ScatteredDrifter/BullIso/pcb/pcb.kicad_sch

## KiCad design pcb/pcb.kicad_sch (2023-05-31)

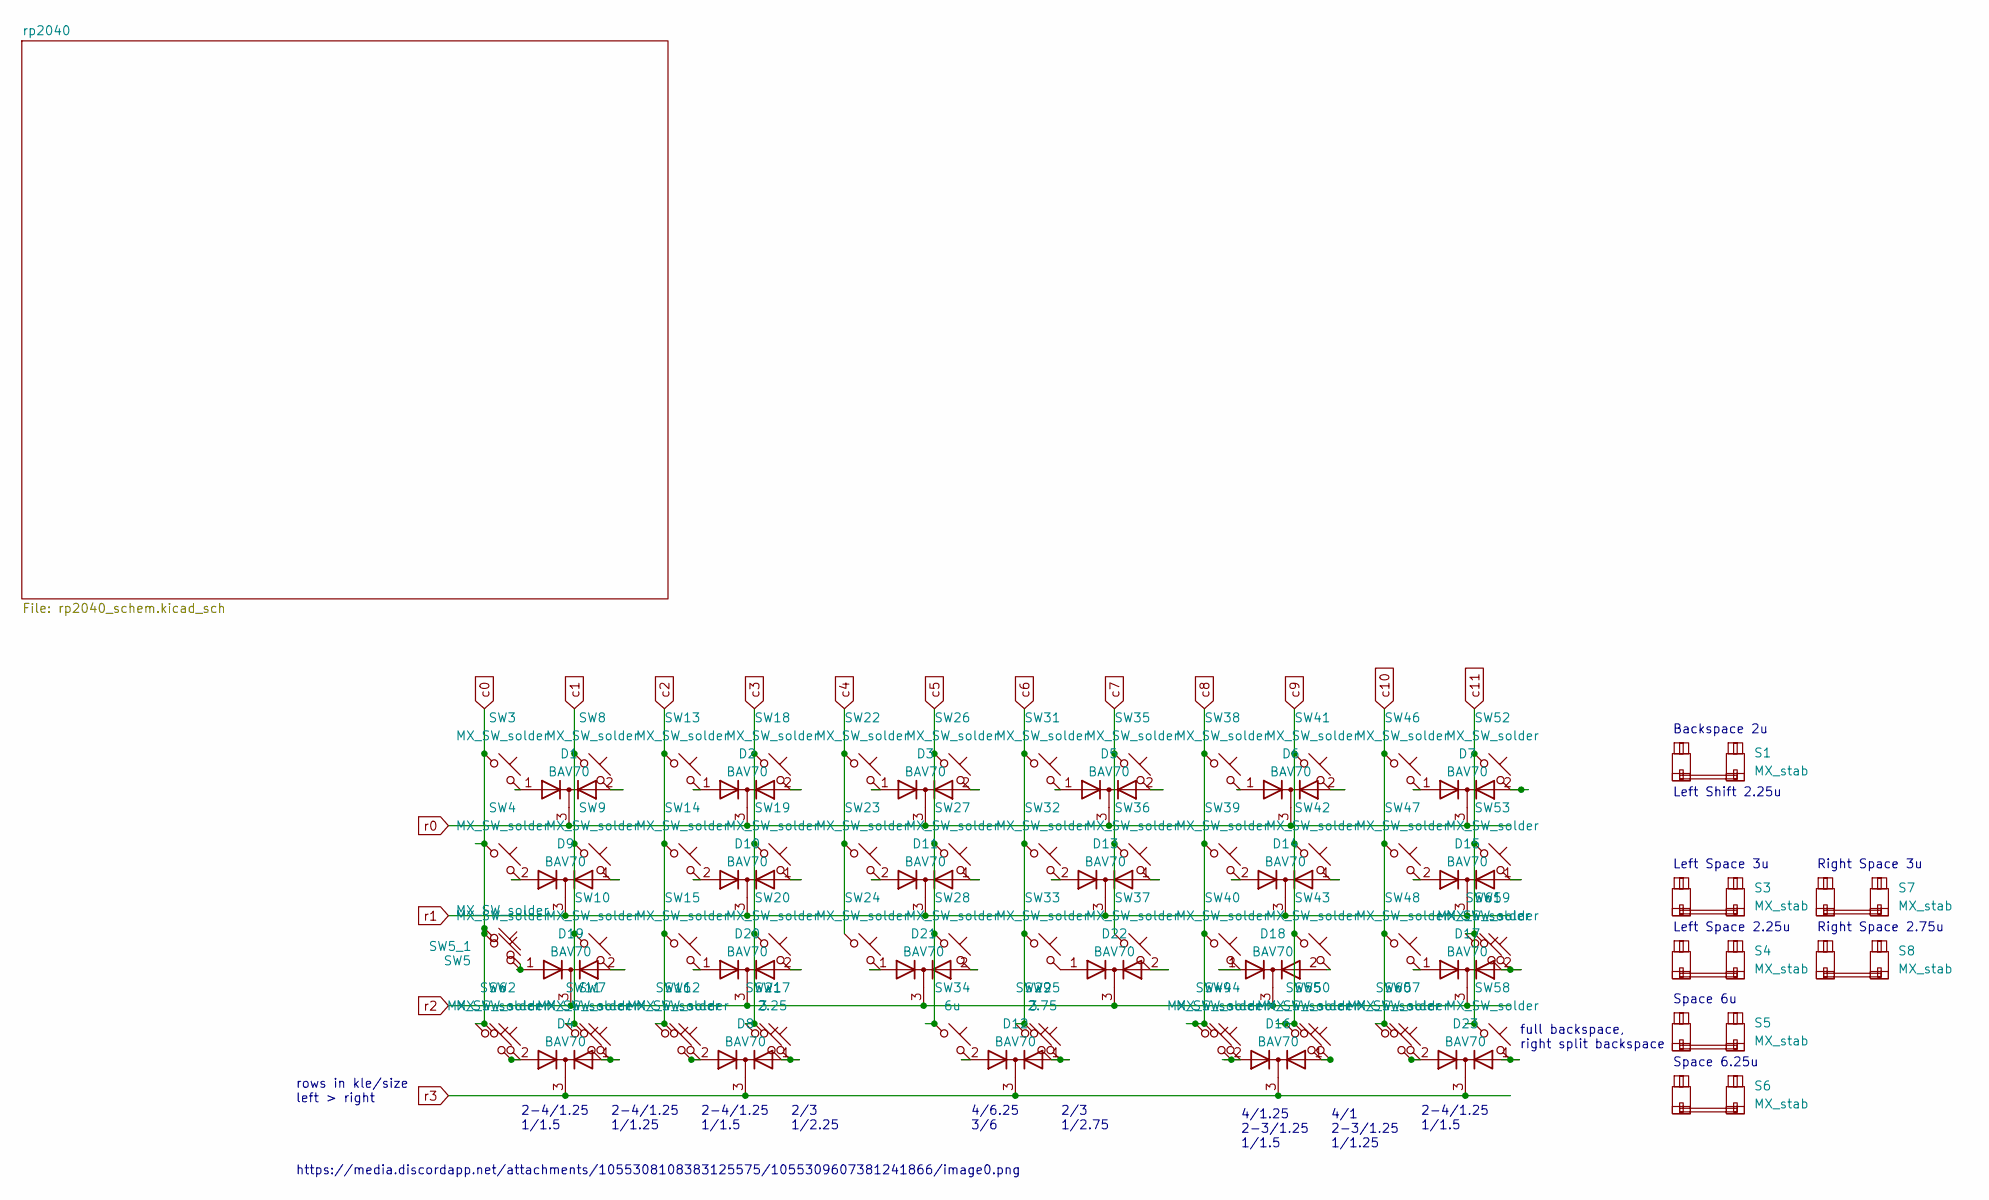
[picture p7: schematic pcb.kicad_sch]

Parts:
D1, D2, D3, D4, D5, D6, D7, D8, D9, D10, D11, D12, D13, D14, D15, D16, D17, D18, D19, D20, D21, D22, D23: BAV70; SOT-23; LCSC C68978
S1: MX_stab; STAB_MX_P_2u
S3, S7: MX_stab; STAB_MX_P_3u
S4: MX_stab; STAB_MX_P_2.25u
S5: MX_stab; STAB_MX_6u
S6: MX_stab; STAB_MX_6.25u
S8: MX_stab; STAB_MX_P_2.75u
SW2, SW3, SW4, SW5, SW5_1, SW6, SW7, SW8, SW9, SW10, SW11, SW12, SW13, SW14, SW15, SW16, SW18, SW19, SW20, SW22, SW23, SW24, SW26, SW27, SW28, SW31, SW32, SW33, SW35, SW36, SW37, SW38, SW39, SW40, SW41, SW42, SW43, SW44, SW46, SW47, SW48, SW49, SW50, SW52, SW53, SW55, SW57, SW58, SW59, SW60, SW61: MX_SW_solder; SW_MX_1u
SW17: 2.25; SW_MX_1u
SW21, SW29: 3; SW_MX_1u
SW25: 2.75; SW_MX_1u
SW34: 6u; SW_MX_1u

Connections:
unnamed: D1.1 (A), SW3.2
unnamed: D1.2 (A), SW8.2
unnamed: D2.1 (A), SW13.2
unnamed: D2.2 (A), SW18.2
unnamed: D3.1 (A), SW22.2
unnamed: D3.2 (A), SW26.2
unnamed: D4.1 (A), SW7.2, SW11.2
unnamed: D4.2 (A), SW2.2, SW6.2
unnamed: D5.1 (A), SW31.2
unnamed: D5.2 (A), SW35.2
unnamed: D6.1 (A), SW38.2
unnamed: D6.2 (A), SW41.2
unnamed: D7.1 (A), SW46.2
unnamed: D7.2 (A), SW52.2
unnamed: D8.1 (A), SW17.2, SW21.2
unnamed: D8.2 (A), SW12.2, SW16.2
unnamed: D9.1 (A), SW9.2
unnamed: D9.2 (A), SW4.2
unnamed: D10.1 (A), SW19.2
unnamed: D10.2 (A), SW14.2
unnamed: D11.1 (A), SW27.2
unnamed: D11.2 (A), SW23.2
unnamed: D12.1 (A), SW25.2, SW29.2
unnamed: D12.2 (A), SW34.2
unnamed: D13.1 (A), SW36.2
unnamed: D13.2 (A), SW32.2
unnamed: D14.1 (A), SW42.2
unnamed: D14.2 (A), SW39.2
unnamed: D15.1 (A), SW53.2
unnamed: D15.2 (A), SW47.2
unnamed: D16.1 (A), SW50.2, SW55.2
unnamed: D17.1 (A), SW48.2
unnamed: D17.2 (A), SW59.2, SW61.2
unnamed: D18.1 (A), SW40.2
unnamed: D18.2 (A), SW43.2
unnamed: D19.1 (A), SW5.2, SW5_1.2
unnamed: D19.2 (A), SW10.2
unnamed: D20.1 (A), SW15.2
unnamed: D20.2 (A), SW20.2
unnamed: D21.1 (A), SW24.2
unnamed: D21.2 (A), SW28.2
unnamed: D22.1 (A), SW33.2
unnamed: D22.2 (A), SW37.2
unnamed: D23.1 (A), SW58.2
unnamed: D23.2 (A), SW57.2, SW60.2
unnamed: SW44.2, SW49.2
c0: SW2.1, SW3.1, SW4.1, SW5.1, SW5_1.1, SW6.1
c1: SW7.1, SW8.1, SW9.1, SW10.1, SW11.1
c2: SW12.1, SW13.1, SW14.1, SW15.1, SW16.1
c3: SW17.1, SW18.1, SW19.1, SW20.1, SW21.1
c4: SW22.1, SW23.1, SW24.1
c5: SW26.1, SW27.1, SW28.1, SW34.1
c6: SW25.1, SW29.1, SW31.1, SW32.1, SW33.1
c7: SW35.1, SW36.1, SW37.1
c8: SW38.1, SW39.1, SW40.1, SW44.1, SW49.1
c9: SW41.1, SW42.1, SW43.1, SW50.1, SW55.1
c10: SW46.1, SW47.1, SW48.1, SW57.1, SW60.1
c11: SW52.1, SW53.1, SW58.1, SW59.1, SW61.1
r0: D1.3 (K), D2.3 (K), D3.3 (K), D5.3 (K), D6.3 (K), D7.3 (K)
r1: D9.3 (K), D10.3 (K), D11.3 (K), D13.3 (K), D14.3 (K), D15.3 (K)
r2: D17.3 (K), D18.3 (K), D19.3 (K), D20.3 (K), D21.3 (K), D22.3 (K)
r3: D4.3 (K), D8.3 (K), D12.3 (K), D16.3 (K), D23.3 (K)

Notes on the sheet:
Backspace 2u
https://media.discordapp.net/attachments/1055308108383125575/1055309607381241866/image0.png
2-4/1.25 1/1.5
Left Space 3u
4/1.25 2-3/1.25 1/1.5
full backspace, right split backspace
2-4/1.25 1/1.25
2/3 1/2.75
rows in kle/size left > right
Right Space 3u
Space 6.25u
2/3 1/2.25
4/1 2-3/1.25 1/1.25
Space 6u
Left Shift 2.25u
4/6.25 3/6
Right Space 2.75u
Left Space 2.25u
